bad64/OpenFightStick/Ork/220x220mm/STL/Top Panel/WASD/WASD top right.stl

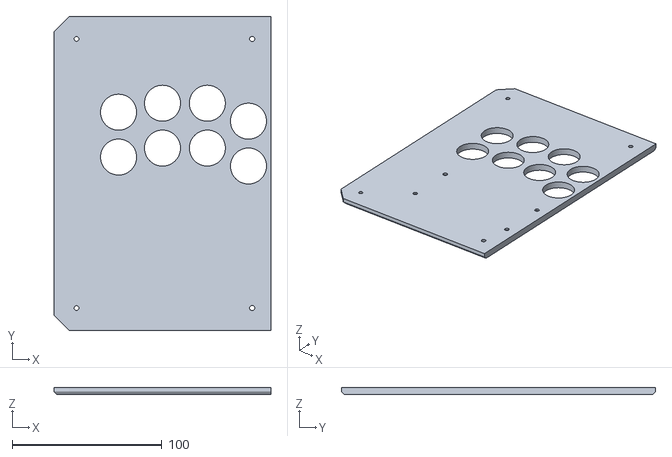
[picture p20: CAD file, 2024-07-23]
Ork/220x220mm/STL/Top Panel/WASD/WASD top right.stl
145.0 x 210.0 x 5.00
