bad64/OpenFightStick/Ork/300x300mm/STL/bottom.stl

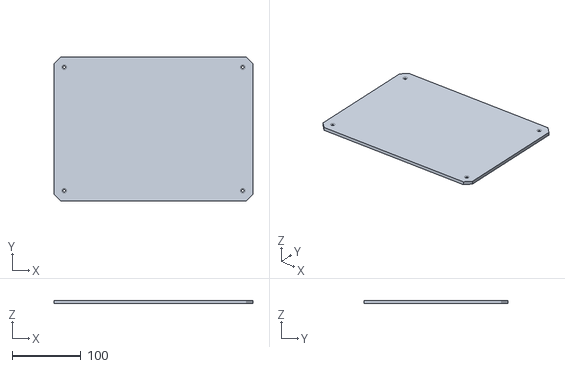
[picture p21: CAD file, 2024-07-23]
Ork/300x300mm/STL/bottom.stl
290.0 x 210.0 x 5.00
