bad64/OpenFightStick/Ork/Common/Brook Spacer.stl

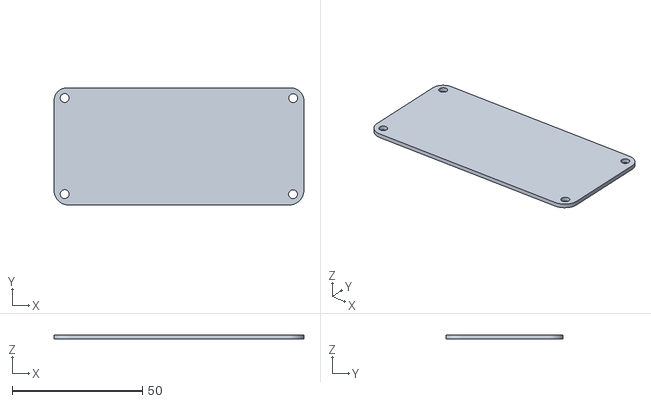
[picture p22: CAD file, 2024-11-10]
Ork/Common/Brook Spacer.stl
96.0 x 45.0 x 1.60
