bad64/OpenFightStick/Chimera/STL/Chimera_Front.stl

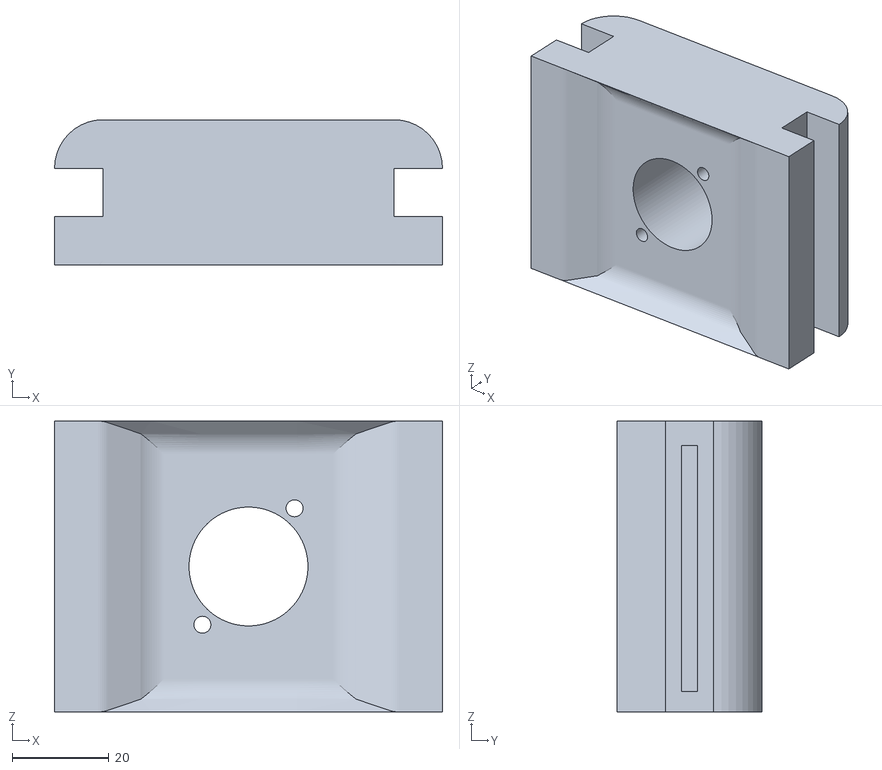
[picture p23: CAD file, 2024-07-23]
Chimera/STL/Chimera_Front.stl
80.0 x 30.0 x 60.0
