bad64/OpenFightStick/Chimera/STL/Top/Left/Chimera_TopLeft_NoCollar.stl

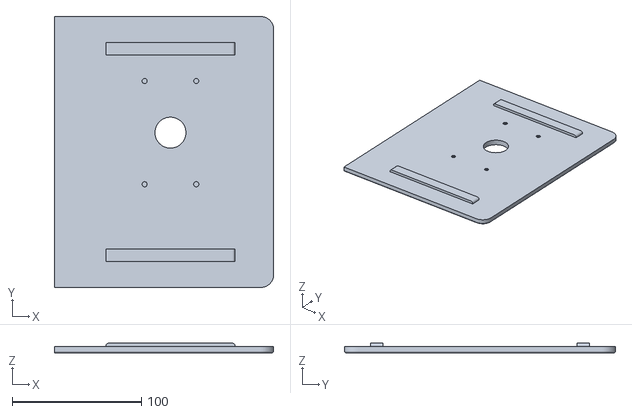
[picture p24: CAD file, 2024-07-23]
Chimera/STL/Top/Left/Chimera_TopLeft_NoCollar.stl
170.0 x 210.0 x 7.50
