bad64/OpenFightStick/Ork/220x220mm/STL/Body Right.stl

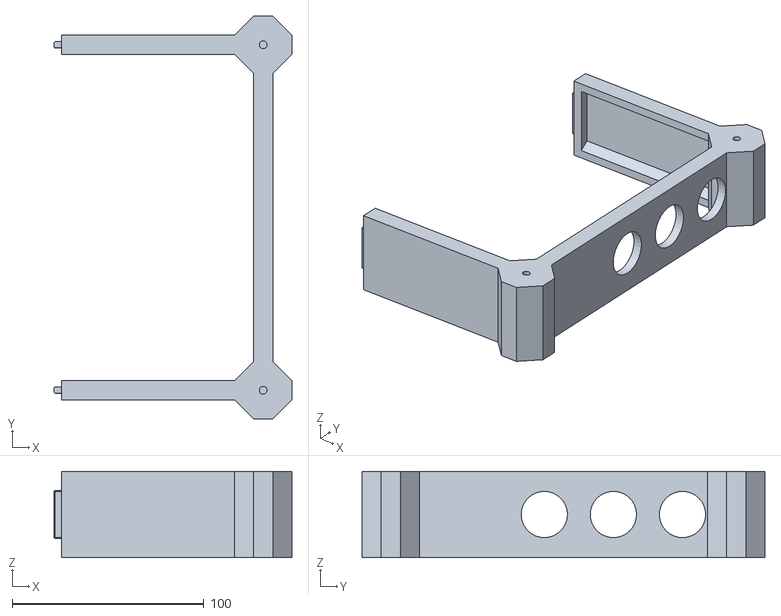
[picture p25: CAD file, 2024-11-10]
Ork/220x220mm/STL/Body Right.stl
124.0 x 210.0 x 45.0
