bad64/OpenFightStick/Ork/Common/Surround.stl

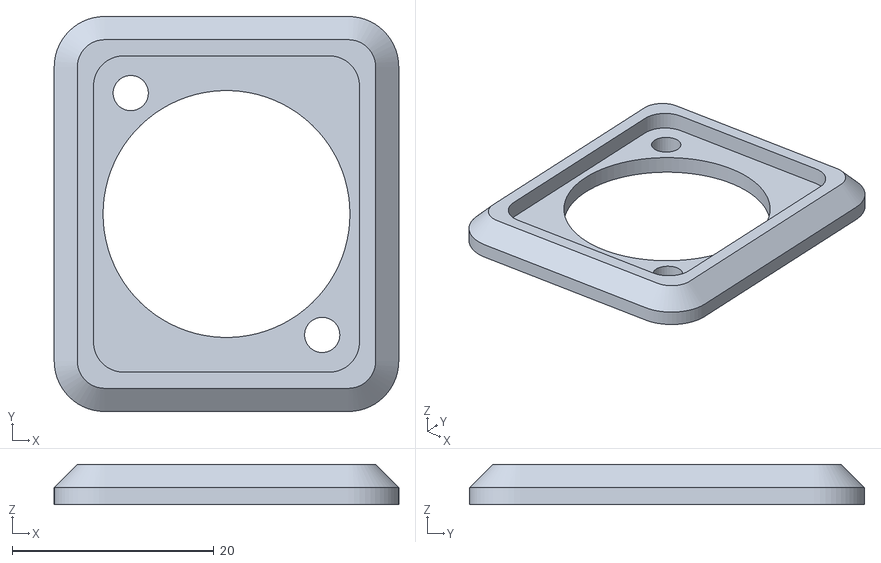
[picture p26: CAD file, 2024-11-10]
Ork/Common/Surround.stl
34.2 x 39.2 x 4.00
