bad64/OpenFightStick/Chimera/STL/Chimera_Bottom_Right.stl

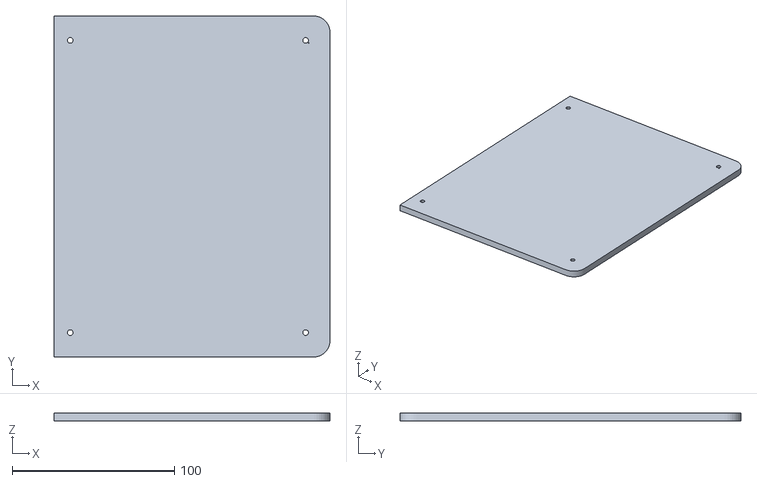
[picture p27: CAD file, 2024-07-23]
Chimera/STL/Chimera_Bottom_Right.stl
170.0 x 210.0 x 5.00
