bad64/OpenFightStick/Ork/220x220mm/STL/Body Back Joiner.stl

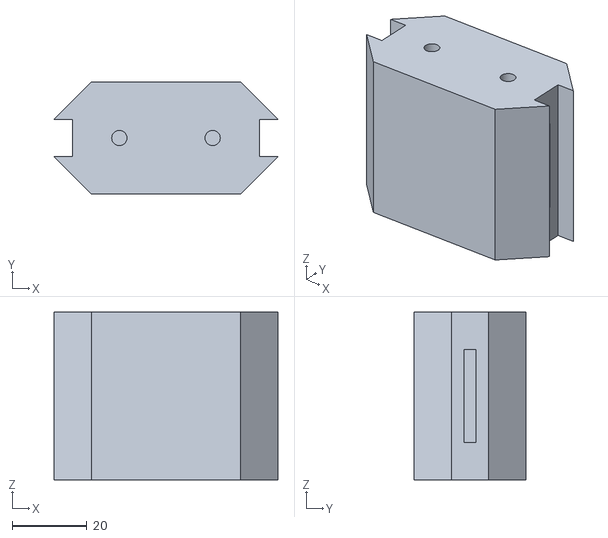
[picture p28: CAD file, 2024-11-10]
Ork/220x220mm/STL/Body Back Joiner.stl
60.0 x 30.0 x 45.0
