bad64/OpenFightStick/Ork/220x220mm/STL/Bottom.stl

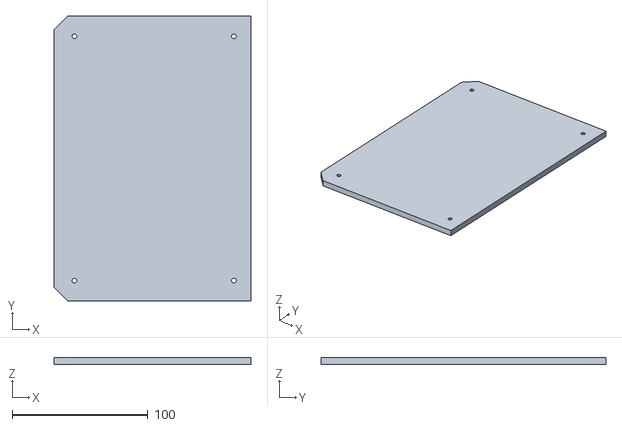
[picture p30: CAD file, 2024-07-23]
Ork/220x220mm/STL/Bottom.stl
145.0 x 210.0 x 5.00
