bad64/OpenFightStick/Chimera/STL/Chimera_Back.stl

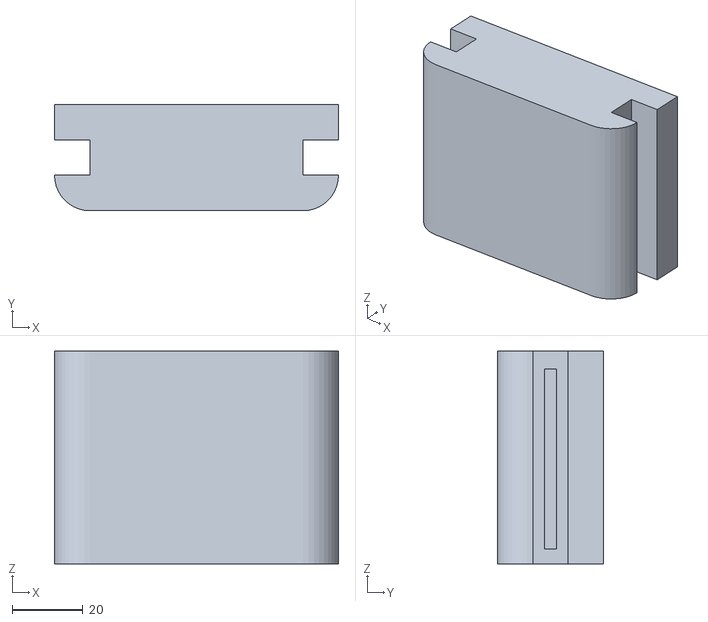
[picture p31: CAD file, 2024-07-23]
Chimera/STL/Chimera_Back.stl
80.0 x 30.0 x 60.0
